pingyun001/LimeRC/STRUCTOR/RemoteController/成品零件/锂电池603450.SLDPRT

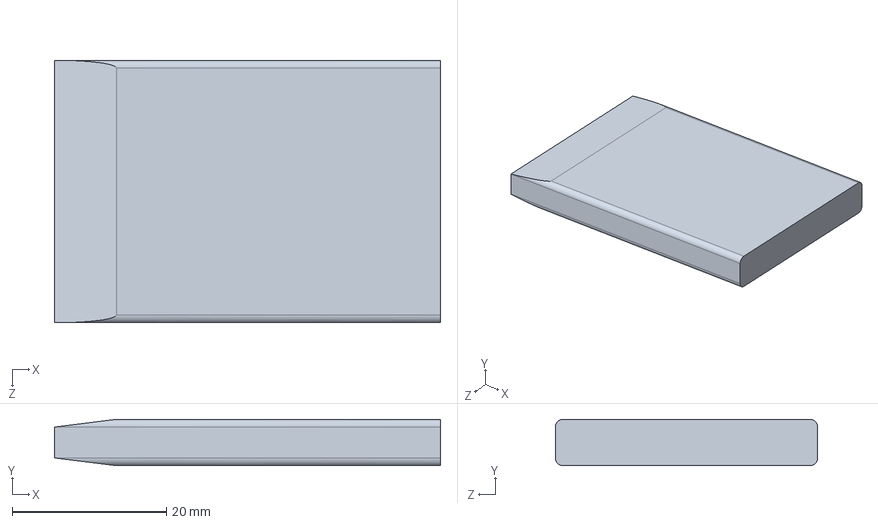
[picture p37: CAD file, 2025-12-01]
STRUCTOR/RemoteController/成品零件/锂电池603450.SLDPRT
50.0 x 6.00 x 34.0 mm
