pingyun001/LimeRC/STRUCTOR/RemoteController/打印件/摇杆帽打印.3MF

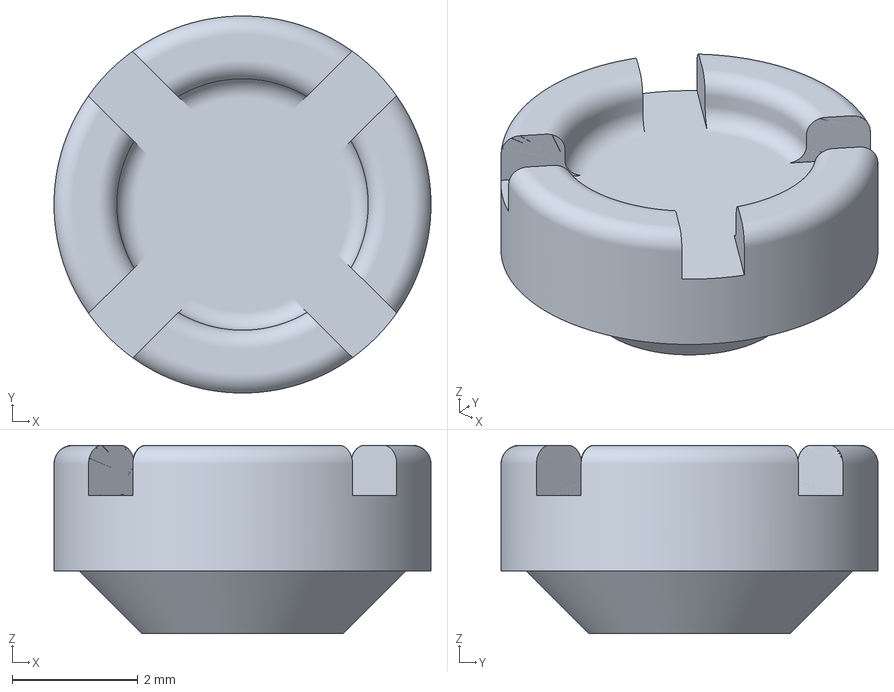
[picture p38: CAD file, 2025-12-01]
STRUCTOR/RemoteController/打印件/摇杆帽打印.3MF
6.00 x 6.00 x 3.00 mm
