pingyun001/LimeRC/STRUCTOR/ScreenSubBoard/1.3寸240屏幕焊接1.STEP

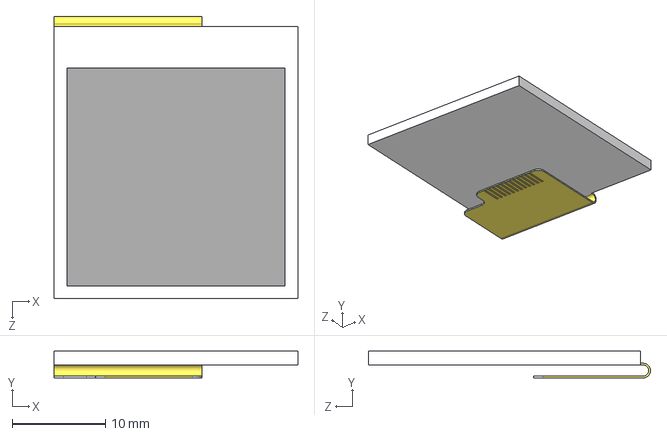
[picture p39: CAD file, 2025-12-01]
STRUCTOR/ScreenSubBoard/1.3寸240屏幕焊接1.STEP
26.2 x 2.89 x 30.3 mm
