pingyun001/LimeRC/STRUCTOR/RemoteController/侧框打印.SLDPRT

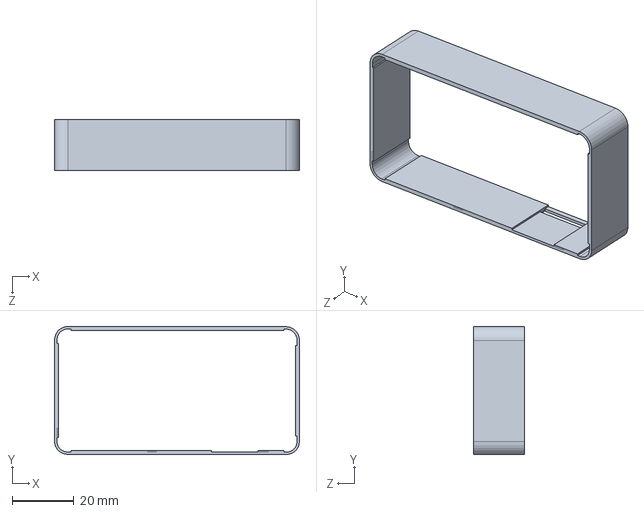
[picture p40: CAD file, 2025-12-01]
STRUCTOR/RemoteController/侧框打印.SLDPRT
79.5 x 41.5 x 16.7 mm
