pingyun001/LimeRC/STRUCTOR/RemoteController/打印件/中心打印支架上.SLDPRT

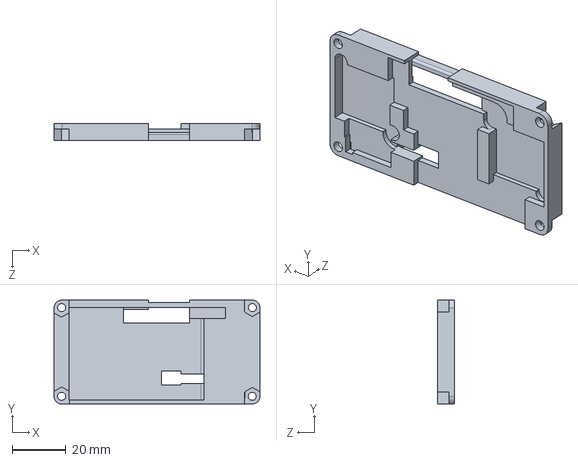
[picture p41: CAD file, 2025-12-01]
STRUCTOR/RemoteController/打印件/中心打印支架上.SLDPRT
76.7 x 38.7 x 6.40 mm
