pingyun001/LimeRC/STRUCTOR/ScreenSubBoard/3D摇杆.SLDPRT

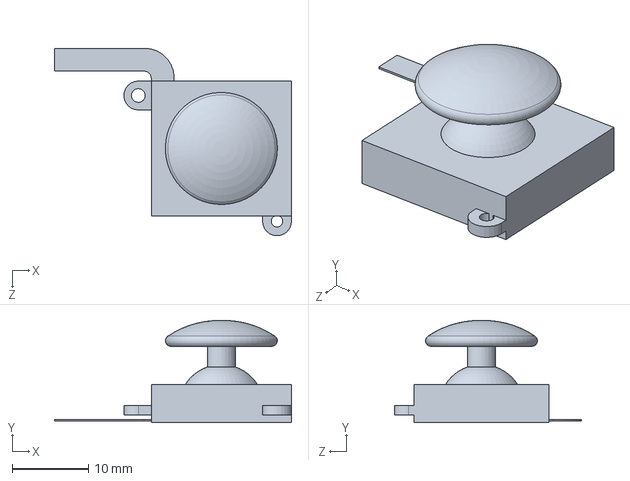
[picture p42: CAD file, 2025-12-01]
STRUCTOR/ScreenSubBoard/3D摇杆.SLDPRT
31.1 x 13.4 x 24.6 mm
