pingyun001/LimeRC/STRUCTOR/RemoteController/成品零件/锂电池102550.SLDPRT

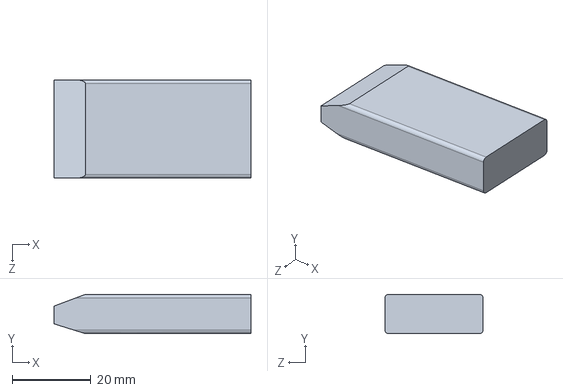
[picture p43: CAD file, 2025-12-01]
STRUCTOR/RemoteController/成品零件/锂电池102550.SLDPRT
50.0 x 10.0 x 25.0 mm
