pingyun001/LimeRC/STRUCTOR/RemoteController/打印件/底壳打印.SLDPRT

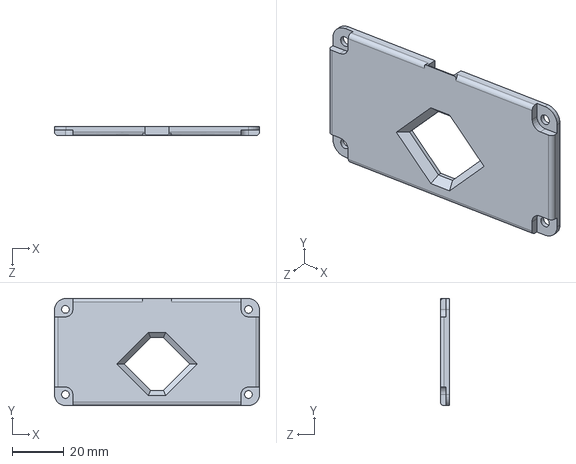
[picture p44: CAD file, 2025-12-01]
STRUCTOR/RemoteController/打印件/底壳打印.SLDPRT
79.5 x 41.5 x 3.50 mm
