pingyun001/LimeRC/STRUCTOR/ScreenSubBoard/摇杆模组PCB定位件.DXF

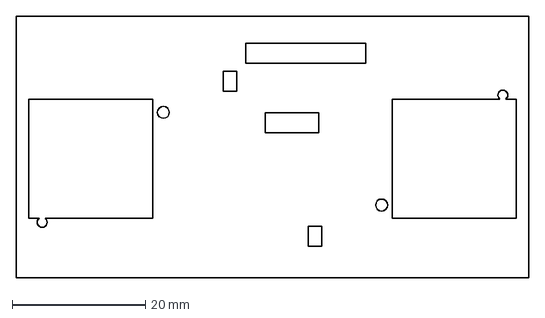
[picture p45: CAD file, 2025-12-01]
STRUCTOR/ScreenSubBoard/摇杆模组PCB定位件.DXF
77.0 x 39.2 mm
