pingyun001/LimeRC/STRUCTOR/RemoteController/打印件/中心打印支架下.SLDPRT

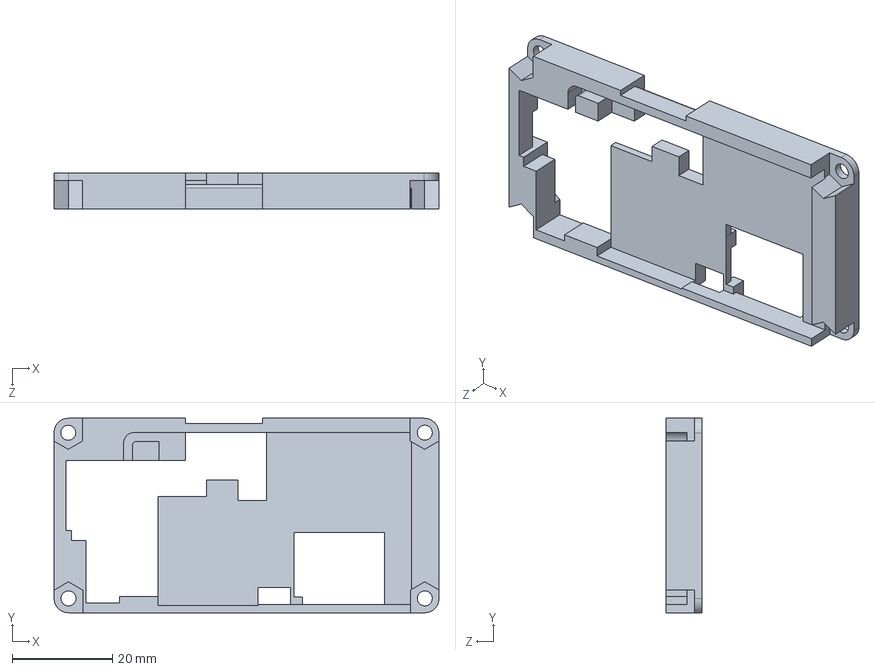
[picture p46: CAD file, 2025-12-01]
STRUCTOR/RemoteController/打印件/中心打印支架下.SLDPRT
76.7 x 38.8 x 7.10 mm
