pingyun001/LimeRC/STRUCTOR/RemoteController/打印件/顶壳打印.SLDPRT

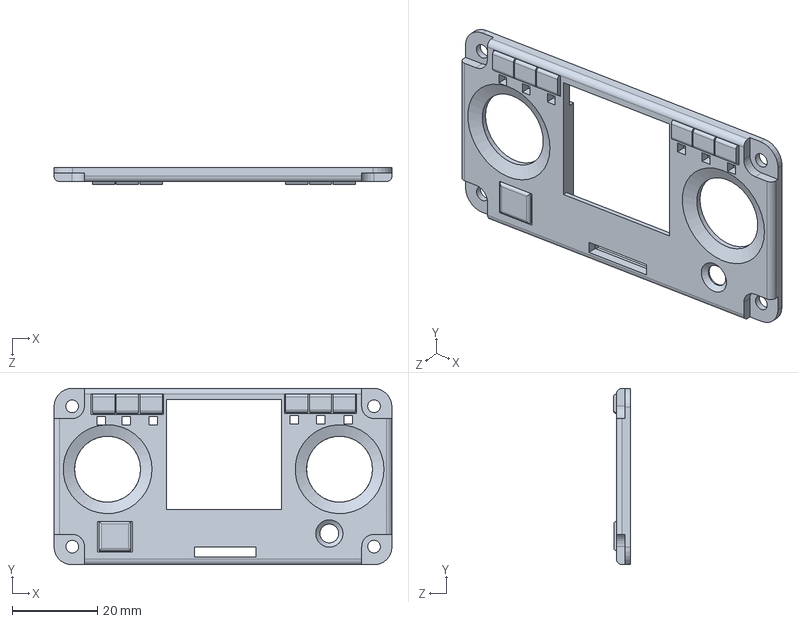
[picture p47: CAD file, 2025-12-01]
STRUCTOR/RemoteController/打印件/顶壳打印.SLDPRT
79.5 x 41.5 x 4.00 mm
