pingyun001/LimeRC/STRUCTOR/ScreenSubBoard/1.3寸240屏幕焊接.SLDPRT

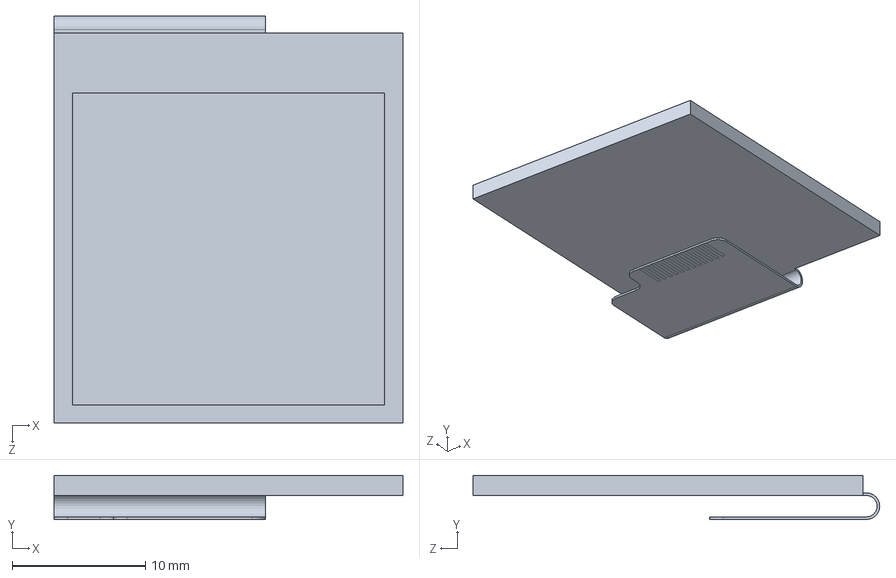
[picture p48: CAD file, 2025-12-01]
STRUCTOR/ScreenSubBoard/1.3寸240屏幕焊接.SLDPRT
26.2 x 3.30 x 30.5 mm
