pingyun001/LimeRC/SOFTWARE/LimeCam_Release/Core/Src/usart.c

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
/* Includes ------------------------------------------------------------------*/
#include "usart.h"

/* USER CODE BEGIN 0 */
#include "stdio.h"

#if defined(__ARMCC_VERSION) && (__ARMCC_VERSION > 6000000)
// V5编译器
#define COMPILER_IS_V6	1
#else
// V6编译器
#define COMPILER_IS_V5	1
#endif

#ifdef COMPILER_IS_V6
#if !defined(__MICROLIB)
__asm (".global __use_no_semihosting\n\t");
void _sys_exit(int x) //避免使用半主机模式
{
  x = x;
}
//__use_no_semihosting was requested, but _ttywrch was 
void _ttywrch(int ch)
{
    ch = ch;
}
FILE __stdout;
#endif		//!defined(__MICROLIB)

#if defined ( __GNUC__ ) && !defined (__clang__) 
#define PUTCHAR_PROTOTYPE int __io_putchar(int ch)
#else
#define PUTCHAR_PROTOTYPE int fputc(int ch, FILE *f)
#endif 
PUTCHAR_PROTOTYPE
{
  /* 实现串口发送一个字节数据的函数 */
  //serial_write(&serial1, (uint8_t)ch); //发送一个自己的数据到串口
	while((UART5 -> SR & 0X40) == 0){}
    UART5->DR = (uint8_t )ch;
  return ch;
}
#endif
#ifdef COMPILER_IS_V5
#pragma import(__use_no_semihosting)                             
struct __FILE { 
    int handle; 
}; 

FILE __stdout;          
void _sys_exit(int x) { 
    x = x; 
}
//重定向printf到串口7（A板上标注有7的位置）
int fputc(int ch, FILE *f){      
    while((UART5 -> SR & 0X40) == 0){}
    UART5->DR = (uint8_t )ch;
    return ch;
}
#endif	//(COMPILER_IS_V5)

#include <stdio.h>
#include <stdarg.h>
int LEPrintf(const char *format, ...) 
{
    char buffer[128]; // 缓冲区，用于存储格式化后的字符串
    va_list args;
    int length;

    // 初始化可变参数列表
    va_start(args, format);

    // 使用 snprintf 格式化字符串
    length = vsnprintf(buffer, sizeof(buffer), format, args);

    // 结束可变参数处理
    va_end(args);

    // 如果字符串过长，截断输出
    if (length > sizeof(buffer) - 1) {
        length = sizeof(buffer) - 1;
    }

    // 通过 UART 发送格式化后的字符串
		HAL_UART_Transmit(&huart1, (uint8_t *)"[LEP]:", 6, 500);
    HAL_UART_Transmit(&huart1, (uint8_t *)buffer, length, 500);

    return length; // 返回实际输出的字符数
}

/* USER CODE END 0 */

UART_HandleTypeDef huart5;
UART_HandleTypeDef huart1;
UART_HandleTypeDef huart2;
UART_HandleTypeDef huart3;

/* UART5 init function */
void MX_UART5_Init(void)
{

  huart5.Instance = UART5;
  huart5.Init.BaudRate = 921600;
  huart5.Init.WordLength = UART_WORDLENGTH_8B;
  huart5.Init.StopBits = UART_STOPBITS_1;
  huart5.Init.Parity = UART_PARITY_NONE;
  huart5.Init.Mode = UART_MODE_TX_RX;
  huart5.Init.HwFlowCtl = UART_HWCONTROL_NONE;
  huart5.Init.OverSampling = UART_OVERSAMPLING_16;
  if (HAL_UART_Init(&huart5) != HAL_OK)
  {
    Error_Handler();
  }
}
/* USART1 init function */

void MX_USART1_UART_Init(void)
{

  huart1.Instance = USART1;
  huart1.Init.BaudRate = 115200;
  huart1.Init.WordLength = UART_WORDLENGTH_8B;
  huart1.Init.StopBits = UART_STOPBITS_1;
  huart1.Init.Parity = UART_PARITY_NONE;
  huart1.Init.Mode = UART_MODE_TX_RX;
  huart1.Init.HwFlowCtl = UART_HWCONTROL_NONE;
  huart1.Init.OverSampling = UART_OVERSAMPLING_16;
  if (HAL_UART_Init(&huart1) != HAL_OK)
  {
    Error_Handler();
  }
}
/* USART2 init function */

void MX_USART2_UART_Init(void)
{

  huart2.Instance = USART2;
  huart2.Init.BaudRate = 115200;
  huart2.Init.WordLength = UART_WORDLENGTH_8B;
  huart2.Init.StopBits = UART_STOPBITS_1;
  huart2.Init.Parity = UART_PARITY_NONE;
  huart2.Init.Mode = UART_MODE_TX_RX;
  huart2.Init.HwFlowCtl = UART_HWCONTROL_NONE;
  huart2.Init.OverSampling = UART_OVERSAMPLING_16;
  if (HAL_UART_Init(&huart2) != HAL_OK)
  {
    Error_Handler();
  }
}
/* USART3 init function */

void MX_USART3_UART_Init(void)
{

  huart3.Instance = USART3;
  huart3.Init.BaudRate = 115200;
  huart3.Init.WordLength = UART_WORDLENGTH_8B;
  huart3.Init.StopBits = UART_STOPBITS_1;
  huart3.Init.Parity = UART_PARITY_NONE;
  huart3.Init.Mode = UART_MODE_TX_RX;
  huart3.Init.HwFlowCtl = UART_HWCONTROL_NONE;
  huart3.Init.OverSampling = UART_OVERSAMPLING_16;
  if (HAL_UART_Init(&huart3) != HAL_OK)
  {
    Error_Handler();
  }
}

void HAL_UART_MspInit(UART_HandleTypeDef* uartHandle)
{

  GPIO_InitTypeDef GPIO_InitStruct = {0};
  if(uartHandle->Instance==UART5)
  {
    /* UART5 clock enable */
    __HAL_RCC_UART5_CLK_ENABLE();

    __HAL_RCC_GPIOC_CLK_ENABLE();
    __HAL_RCC_GPIOD_CLK_ENABLE();
    /**UART5 GPIO Configuration
    PC12     ------> UART5_TX
    PD2     ------> UART5_RX
    */
    GPIO_InitStruct.Pin = GPIO_PIN_12;
    GPIO_InitStruct.Mode = GPIO_MODE_AF_PP;
    GPIO_InitStruct.Pull = GPIO_NOPULL;
    GPIO_InitStruct.Speed = GPIO_SPEED_FREQ_VERY_HIGH;
    GPIO_InitStruct.Alternate = GPIO_AF8_UART5;
    HAL_GPIO_Init(GPIOC, &GPIO_InitStruct);

    GPIO_InitStruct.Pin = GPIO_PIN_2;
    GPIO_InitStruct.Mode = GPIO_MODE_AF_PP;
    GPIO_InitStruct.Pull = GPIO_NOPULL;
    GPIO_InitStruct.Speed = GPIO_SPEED_FREQ_VERY_HIGH;
    GPIO_InitStruct.Alternate = GPIO_AF8_UART5;
    HAL_GPIO_Init(GPIOD, &GPIO_InitStruct);

  }
  else if(uartHandle->Instance==USART1)
  {
    /* USART1 clock enable */
    __HAL_RCC_USART1_CLK_ENABLE();

    __HAL_RCC_GPIOA_CLK_ENABLE();
    /**USART1 GPIO Configuration
    PA9     ------> USART1_TX
    PA10     ------> USART1_RX
    */
    GPIO_InitStruct.Pin = GPIO_PIN_9|GPIO_PIN_10;
    GPIO_InitStruct.Mode = GPIO_MODE_AF_PP;
    GPIO_InitStruct.Pull = GPIO_NOPULL;
    GPIO_InitStruct.Speed = GPIO_SPEED_FREQ_VERY_HIGH;
    GPIO_InitStruct.Alternate = GPIO_AF7_USART1;
    HAL_GPIO_Init(GPIOA, &GPIO_InitStruct);

  }
  else if(uartHandle->Instance==USART2)
  {
    /* USART2 clock enable */
    __HAL_RCC_USART2_CLK_ENABLE();

    __HAL_RCC_GPIOA_CLK_ENABLE();
    /**USART2 GPIO Configuration
    PA2     ------> USART2_TX
    PA3     ------> USART2_RX
    */
    GPIO_InitStruct.Pin = GPIO_PIN_2|GPIO_PIN_3;
    GPIO_InitStruct.Mode = GPIO_MODE_AF_PP;
    GPIO_InitStruct.Pull = GPIO_NOPULL;
    GPIO_InitStruct.Speed = GPIO_SPEED_FREQ_VERY_HIGH;
    GPIO_InitStruct.Alternate = GPIO_AF7_USART2;
    HAL_GPIO_Init(GPIOA, &GPIO_InitStruct);

  }
  else if(uartHandle->Instance==USART3)
  {
    /* USART3 clock enable */
    __HAL_RCC_USART3_CLK_ENABLE();

    __HAL_RCC_GPIOD_CLK_ENABLE();
    /**USART3 GPIO Configuration
    PD8     ------> USART3_TX
    PD9     ------> USART3_RX
    */
    GPIO_InitStruct.Pin = GPIO_PIN_8|GPIO_PIN_9;
    GPIO_InitStruct.Mode = GPIO_MODE_AF_PP;
    GPIO_InitStruct.Pull = GPIO_NOPULL;
    GPIO_InitStruct.Speed = GPIO_SPEED_FREQ_VERY_HIGH;
    GPIO_InitStruct.Alternate = GPIO_AF7_USART3;
    HAL_GPIO_Init(GPIOD, &GPIO_InitStruct);

    /* USART3 interrupt Init */
    HAL_NVIC_SetPriority(USART3_IRQn, 10, 0);
    HAL_NVIC_EnableIRQ(USART3_IRQn);
  }
}

void HAL_UART_MspDeInit(UART_HandleTypeDef* uartHandle)
{

  if(uartHandle->Instance==UART5)
  {
    /* Peripheral clock disable */
    __HAL_RCC_UART5_CLK_DISABLE();

    /**UART5 GPIO Configuration
    PC12     ------> UART5_TX
    PD2     ------> UART5_RX
    */
    HAL_GPIO_DeInit(GPIOC, GPIO_PIN_12);

    HAL_GPIO_DeInit(GPIOD, GPIO_PIN_2);

  }
  else if(uartHandle->Instance==USART1)
  {
    /* Peripheral clock disable */
    __HAL_RCC_USART1_CLK_DISABLE();

    /**USART1 GPIO Configuration
    PA9     ------> USART1_TX
    PA10     ------> USART1_RX
    */
    HAL_GPIO_DeInit(GPIOA, GPIO_PIN_9|GPIO_PIN_10);

  }
  else if(uartHandle->Instance==USART2)
  {
    /* Peripheral clock disable */
    __HAL_RCC_USART2_CLK_DISABLE();

    /**USART2 GPIO Configuration
    PA2     ------> USART2_TX
    PA3     ------> USART2_RX
    */
    HAL_GPIO_DeInit(GPIOA, GPIO_PIN_2|GPIO_PIN_3);

  }
  else if(uartHandle->Instance==USART3)
  {
    /* Peripheral clock disable */
    __HAL_RCC_USART3_CLK_DISABLE();

    /**USART3 GPIO Configuration
    PD8     ------> USART3_TX
    PD9     ------> USART3_RX
    */
    HAL_GPIO_DeInit(GPIOD, GPIO_PIN_8|GPIO_PIN_9);

    /* USART3 interrupt Deinit */
    HAL_NVIC_DisableIRQ(USART3_IRQn);
  }
}
