pingyun001/LimeRC/SOFTWARE/LimeMainBoard_Release/Core/Src/usart.c

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
/* Includes ------------------------------------------------------------------*/
#include "usart.h"

/* USER CODE BEGIN 0 */
#include <stdio.h>
#include <stdarg.h>
int LEprintf(const char *format, ...)
{
    char buffer[128];
    va_list args;
    int length;

    va_start(args, format);

    length = vsnprintf(buffer, sizeof(buffer), format, args);

    va_end(args);

    if (length > sizeof(buffer) - 1) {
        length = sizeof(buffer) - 1;
    }

    HAL_UART_Transmit(&huart1, (uint8_t *)buffer, length, HAL_MAX_DELAY);

    return length;
}

#include "lvgl.h"
#include <string.h>
void lime_lvgl_print(lv_log_level_t level, const char * buf)
{
	LEprintf("%d,%s", level, buf);
}

/* USER CODE END 0 */

UART_HandleTypeDef huart4;
UART_HandleTypeDef huart1;
DMA_HandleTypeDef hdma_uart4_rx;

/* UART4 init function */
void MX_UART4_Init(void)
{

  huart4.Instance = UART4;
  huart4.Init.BaudRate = 115200;
  huart4.Init.WordLength = UART_WORDLENGTH_8B;
  huart4.Init.StopBits = UART_STOPBITS_1;
  huart4.Init.Parity = UART_PARITY_NONE;
  huart4.Init.Mode = UART_MODE_TX_RX;
  huart4.Init.HwFlowCtl = UART_HWCONTROL_NONE;
  huart4.Init.OverSampling = UART_OVERSAMPLING_16;
  huart4.Init.OneBitSampling = UART_ONE_BIT_SAMPLE_DISABLE;
  huart4.Init.ClockPrescaler = UART_PRESCALER_DIV1;
  huart4.AdvancedInit.AdvFeatureInit = UART_ADVFEATURE_NO_INIT;
  if (HAL_UART_Init(&huart4) != HAL_OK)
  {
    Error_Handler();
  }
  if (HAL_UARTEx_SetTxFifoThreshold(&huart4, UART_TXFIFO_THRESHOLD_1_8) != HAL_OK)
  {
    Error_Handler();
  }
  if (HAL_UARTEx_SetRxFifoThreshold(&huart4, UART_RXFIFO_THRESHOLD_1_8) != HAL_OK)
  {
    Error_Handler();
  }
  if (HAL_UARTEx_DisableFifoMode(&huart4) != HAL_OK)
  {
    Error_Handler();
  }
}
/* USART1 init function */

void MX_USART1_UART_Init(void)
{

  huart1.Instance = USART1;
  huart1.Init.BaudRate = 921600;
  huart1.Init.WordLength = UART_WORDLENGTH_8B;
  huart1.Init.StopBits = UART_STOPBITS_1;
  huart1.Init.Parity = UART_PARITY_NONE;
  huart1.Init.Mode = UART_MODE_TX_RX;
  huart1.Init.HwFlowCtl = UART_HWCONTROL_NONE;
  huart1.Init.OverSampling = UART_OVERSAMPLING_16;
  huart1.Init.OneBitSampling = UART_ONE_BIT_SAMPLE_DISABLE;
  huart1.Init.ClockPrescaler = UART_PRESCALER_DIV1;
  huart1.AdvancedInit.AdvFeatureInit = UART_ADVFEATURE_NO_INIT;
  if (HAL_UART_Init(&huart1) != HAL_OK)
  {
    Error_Handler();
  }
  if (HAL_UARTEx_SetTxFifoThreshold(&huart1, UART_TXFIFO_THRESHOLD_1_8) != HAL_OK)
  {
    Error_Handler();
  }
  if (HAL_UARTEx_SetRxFifoThreshold(&huart1, UART_RXFIFO_THRESHOLD_1_8) != HAL_OK)
  {
    Error_Handler();
  }
  if (HAL_UARTEx_DisableFifoMode(&huart1) != HAL_OK)
  {
    Error_Handler();
  }
}

void HAL_UART_MspInit(UART_HandleTypeDef* uartHandle)
{

  GPIO_InitTypeDef GPIO_InitStruct = {0};
  RCC_PeriphCLKInitTypeDef PeriphClkInitStruct = {0};
  if(uartHandle->Instance==UART4)
  {
  /** Initializes the peripherals clock
  */
    PeriphClkInitStruct.PeriphClockSelection = RCC_PERIPHCLK_UART4;
    PeriphClkInitStruct.Usart234578ClockSelection = RCC_USART234578CLKSOURCE_D2PCLK1;
    if (HAL_RCCEx_PeriphCLKConfig(&PeriphClkInitStruct) != HAL_OK)
    {
      Error_Handler();
    }

    /* UART4 clock enable */
    __HAL_RCC_UART4_CLK_ENABLE();

    __HAL_RCC_GPIOD_CLK_ENABLE();
    /**UART4 GPIO Configuration
    PD0     ------> UART4_RX
    PD1     ------> UART4_TX
    */
    GPIO_InitStruct.Pin = GPIO_PIN_0|GPIO_PIN_1;
    GPIO_InitStruct.Mode = GPIO_MODE_AF_PP;
    GPIO_InitStruct.Pull = GPIO_NOPULL;
    GPIO_InitStruct.Speed = GPIO_SPEED_FREQ_LOW;
    GPIO_InitStruct.Alternate = GPIO_AF8_UART4;
    HAL_GPIO_Init(GPIOD, &GPIO_InitStruct);

    /* UART4 DMA Init */
    /* UART4_RX Init */
    hdma_uart4_rx.Instance = DMA1_Stream1;
    hdma_uart4_rx.Init.Request = DMA_REQUEST_UART4_RX;
    hdma_uart4_rx.Init.Direction = DMA_PERIPH_TO_MEMORY;
    hdma_uart4_rx.Init.PeriphInc = DMA_PINC_DISABLE;
    hdma_uart4_rx.Init.MemInc = DMA_MINC_ENABLE;
    hdma_uart4_rx.Init.PeriphDataAlignment = DMA_PDATAALIGN_BYTE;
    hdma_uart4_rx.Init.MemDataAlignment = DMA_MDATAALIGN_BYTE;
    hdma_uart4_rx.Init.Mode = DMA_NORMAL;
    hdma_uart4_rx.Init.Priority = DMA_PRIORITY_LOW;
    hdma_uart4_rx.Init.FIFOMode = DMA_FIFOMODE_DISABLE;
    if (HAL_DMA_Init(&hdma_uart4_rx) != HAL_OK)
    {
      Error_Handler();
    }

    __HAL_LINKDMA(uartHandle,hdmarx,hdma_uart4_rx);

    /* UART4 interrupt Init */
    HAL_NVIC_SetPriority(UART4_IRQn, 8, 0);
    HAL_NVIC_EnableIRQ(UART4_IRQn);
  }
  else if(uartHandle->Instance==USART1)
  {
  /** Initializes the peripherals clock
  */
    PeriphClkInitStruct.PeriphClockSelection = RCC_PERIPHCLK_USART1;
    PeriphClkInitStruct.Usart16ClockSelection = RCC_USART16CLKSOURCE_D2PCLK2;
    if (HAL_RCCEx_PeriphCLKConfig(&PeriphClkInitStruct) != HAL_OK)
    {
      Error_Handler();
    }

    /* USART1 clock enable */
    __HAL_RCC_USART1_CLK_ENABLE();

    __HAL_RCC_GPIOA_CLK_ENABLE();
    /**USART1 GPIO Configuration
    PA9     ------> USART1_TX
    PA10     ------> USART1_RX
    */
    GPIO_InitStruct.Pin = GPIO_PIN_9|GPIO_PIN_10;
    GPIO_InitStruct.Mode = GPIO_MODE_AF_PP;
    GPIO_InitStruct.Pull = GPIO_NOPULL;
    GPIO_InitStruct.Speed = GPIO_SPEED_FREQ_LOW;
    GPIO_InitStruct.Alternate = GPIO_AF7_USART1;
    HAL_GPIO_Init(GPIOA, &GPIO_InitStruct);

  }
}

void HAL_UART_MspDeInit(UART_HandleTypeDef* uartHandle)
{

  if(uartHandle->Instance==UART4)
  {
    /* Peripheral clock disable */
    __HAL_RCC_UART4_CLK_DISABLE();

    /**UART4 GPIO Configuration
    PD0     ------> UART4_RX
    PD1     ------> UART4_TX
    */
    HAL_GPIO_DeInit(GPIOD, GPIO_PIN_0|GPIO_PIN_1);

    /* UART4 DMA DeInit */
    HAL_DMA_DeInit(uartHandle->hdmarx);

    /* UART4 interrupt Deinit */
    HAL_NVIC_DisableIRQ(UART4_IRQn);
  }
  else if(uartHandle->Instance==USART1)
  {
    /* Peripheral clock disable */
    __HAL_RCC_USART1_CLK_DISABLE();

    /**USART1 GPIO Configuration
    PA9     ------> USART1_TX
    PA10     ------> USART1_RX
    */
    HAL_GPIO_DeInit(GPIOA, GPIO_PIN_9|GPIO_PIN_10);

  }
}
