pingyun001/LimeRC/SOFTWARE/LimeCam_Release/Bsp/Lime_ov2640map.h

/**
 ****************************************************************************************************
 * @file        atk_mc2640_cfg.h
 * @author      正点原子团队(ALIENTEK)
 * @version     V1.0
 * @date        2022-06-21
 * @brief       ATK-MC2640模块寄存器配置
 * @license     Copyright (c) 2020-2032, 广州市星翼电子科技有限公司
 ****************************************************************************************************
 * @attention
 *
 * 实验平台:正点原子 Mini Pro H750开发板
 * 在线视频:www.yuanzige.com
 * 技术论坛:www.openedv.com
 * 公司网址:www.alientek.com
 * 购买地址:openedv.taobao.com
 *
 ****************************************************************************************************
 */

#ifndef __ATK_MC2640_CFG_H
#define __ATK_MC2640_CFG_H

#include "main.h"

/* 选择ATK-MC2640模块启用的寄存器块
 * 当寄存器0xFF=00时，启用DSP寄存器块
 * 当寄存器0xFF=01时，启用Sensor寄存器块
 */
#define LIME_OV2640_REG_BANK_SEL  LIME_OV2640_REG_DSP_RA_DLMT

/* ATK-MC2640模块DSP寄存器块 */
#define LIME_OV2640_REG_DSP_R_BYPASS         0x05
#define LIME_OV2640_REG_DSP_Qs               0x44
#define LIME_OV2640_REG_DSP_CTRLI            0x50
#define LIME_OV2640_REG_DSP_HSIZE            0x51
#define LIME_OV2640_REG_DSP_VSIZE            0x52
#define LIME_OV2640_REG_DSP_XOFFL            0x53
#define LIME_OV2640_REG_DSP_YOFFL            0x54
#define LIME_OV2640_REG_DSP_VHYX             0x55
#define LIME_OV2640_REG_DSP_DPRP             0x56
#define LIME_OV2640_REG_DSP_TEST             0x57
#define LIME_OV2640_REG_DSP_ZMOW             0x5A
#define LIME_OV2640_REG_DSP_ZMOH             0x5B
#define LIME_OV2640_REG_DSP_ZMHH             0x5C
#define LIME_OV2640_REG_DSP_BPADDR           0x7C
#define LIME_OV2640_REG_DSP_BPDATA           0x7D
#define LIME_OV2640_REG_DSP_CTRL2            0x86
#define LIME_OV2640_REG_DSP_CTRL3            0x87
#define LIME_OV2640_REG_DSP_SIZEL            0x8C
#define LIME_OV2640_REG_DSP_HSIZE8           0xC0
#define LIME_OV2640_REG_DSP_VSIZE8           0xC1
#define LIME_OV2640_REG_DSP_CTRL0            0xC2
#define LIME_OV2640_REG_DSP_CTRL1            0xC3
#define LIME_OV2640_REG_DSP_R_DVP_SP         0xD3
#define LIME_OV2640_REG_DSP_IMAGE_MODE       0xDA
#define LIME_OV2640_REG_DSP_RESET            0xE0
#define LIME_OV2640_REG_DSP_MS_SP            0xF0
#define LIME_OV2640_REG_DSP_SS_ID            0xF7
#define LIME_OV2640_REG_DSP_SS_CTRL          0xF8
#define LIME_OV2640_REG_DSP_MC_BIST          0xF9
#define LIME_OV2640_REG_DSP_MC_AL            0xFA
#define LIME_OV2640_REG_DSP_MC_AH            0xFB
#define LIME_OV2640_REG_DSP_MC_D             0xFC
#define LIME_OV2640_REG_DSP_P_CMD            0xFD
#define LIME_OV2640_REG_DSP_P_STATUS         0xFE
#define LIME_OV2640_REG_DSP_RA_DLMT          0xFF

/* ATK-MC2640模块Sensor寄存器块 */
#define LIME_OV2640_REG_SENSOR_GAIN          0x00
#define LIME_OV2640_REG_SENSOR_COM1          0x03
#define LIME_OV2640_REG_SENSOR_REG04         0x04
#define LIME_OV2640_REG_SENSOR_REG08         0x08
#define LIME_OV2640_REG_SENSOR_COM2          0x09
#define LIME_OV2640_REG_SENSOR_PIDH          0x0A
#define LIME_OV2640_REG_SENSOR_PIDL          0x0B
#define LIME_OV2640_REG_SENSOR_COM3          0x0C
#define LIME_OV2640_REG_SENSOR_COM4          0x0D
#define LIME_OV2640_REG_SENSOR_AEC           0x10
#define LIME_OV2640_REG_SENSOR_CLKRC         0x11
#define LIME_OV2640_REG_SENSOR_COM7          0x12
#define LIME_OV2640_REG_SENSOR_COM8          0x13
#define LIME_OV2640_REG_SENSOR_COM9          0x14
#define LIME_OV2640_REG_SENSOR_COM10         0x15
#define LIME_OV2640_REG_SENSOR_HREFST        0x17
#define LIME_OV2640_REG_SENSOR_HREFEND       0x18
#define LIME_OV2640_REG_SENSOR_VSTRT         0x19
#define LIME_OV2640_REG_SENSOR_VEND          0x1A
#define LIME_OV2640_REG_SENSOR_MIDH          0x1C
#define LIME_OV2640_REG_SENSOR_MIDL          0x1D
#define LIME_OV2640_REG_SENSOR_AEW           0x24
#define LIME_OV2640_REG_SENSOR_AEB           0x25
#define LIME_OV2640_REG_SENSOR_VV            0x26
#define LIME_OV2640_REG_SENSOR_REG2A         0x2A
#define LIME_OV2640_REG_SENSOR_FRARL         0x2B
#define LIME_OV2640_REG_SENSOR_ADDVSL        0x2D
#define LIME_OV2640_REG_SENSOR_ADDVSH        0x2E
#define LIME_OV2640_REG_SENSOR_YAVG          0x2F
#define LIME_OV2640_REG_SENSOR_HSDY          0x30
#define LIME_OV2640_REG_SENSOR_HEDY          0x31
#define LIME_OV2640_REG_SENSOR_REG32         0x32
#define LIME_OV2640_REG_SENSOR_ARCOM2        0x34
#define LIME_OV2640_REG_SENSOR_REG45         0x45
#define LIME_OV2640_REG_SENSOR_FLL           0x46
#define LIME_OV2640_REG_SENSOR_FLH           0x47
#define LIME_OV2640_REG_SENSOR_COM19         0x48
#define LIME_OV2640_REG_SENSOR_ZOOMS         0x49
#define LIME_OV2640_REG_SENSOR_COM22         0x4B
#define LIME_OV2640_REG_SENSOR_COM25         0x4E
#define LIME_OV2640_REG_SENSOR_BD50          0x4F
#define LIME_OV2640_REG_SENSOR_BD60          0x50
#define LIME_OV2640_REG_SENSOR_REG5D         0x5D
#define LIME_OV2640_REG_SENSOR_REG5E         0x5E
#define LIME_OV2640_REG_SENSOR_REG5F         0x5F
#define LIME_OV2640_REG_SENSOR_REG60         0x60
#define LIME_OV2640_REG_SENSOR_HISTO_LOW     0x61
#define LIME_OV2640_REG_SENSOR_HISTO_HIGH    0x62


const uint8_t atk_mc2640_set_yuv422_cfg[][2] = {
    {0xFF, 0x00},
    {0xDA, 0x10},
    {0xD7, 0x03},
    {0xDF, 0x00},
    {0x33, 0x80},
    {0x3C, 0x40},
    {0xE1, 0x77},
    {0x00, 0x00},
};

const uint8_t atk_mc2640_set_jpeg_cfg[][2] = {
    {0xFF, 0x01},
    {0xE0, 0x14},
    {0xE1, 0x77},
    {0xE5, 0x1F},
    {0xD7, 0x03},
    {0xDA, 0x10},
    {0xE0, 0x00},
};

const uint8_t atk_mc2640_set_rgb565_cfg[][2] = {
    {0xFF, 0x00},
    {0xDA, 0x09},
    {0xD7, 0x03},
    {0xDF, 0x02},
    {0x33, 0xA0},
    {0x3C, 0x00},
    {0xE1, 0x67},
    {0xFF, 0x01},
    {0xE0, 0x00},
    {0xE1, 0x00},
    {0xE5, 0x00},
    {0xD7, 0x00},
    {0xDA, 0x00},
    {0xE0, 0x00},
};

const uint8_t Lime_ov2640_SVGA_Config[][2]=
{

	{0xff, 0x01},  // 设置 sensor 寄存器组
	{0x12, 0x80},  // 复位全部寄存
	 
	{0xFF, 0x00},
	{0x2C, 0xFF},
	{0x2E, 0xDF},
	{0xFF, 0x01},
	{0x3C, 0x32},
	{0x11, 0x00},
	{0x09, 0x02},
	{0x04, 0x28},	//翻转0xF8
	{0x13, 0xE5},
	{0x14, 0x48},
	{0x2C, 0x0C},
	{0x33, 0x78},
	{0x3A, 0x33},
	{0x3B, 0xFB},
	{0x3E, 0x00},
	{0x43, 0x11},
	{0x16, 0x10},
	{0x39, 0x92},
	{0x35, 0xDA},
	{0x22, 0x1A},
	{0x37, 0xC3},
	{0x23, 0x00},
	{0x34, 0xC0},
	{0x36, 0x1A},
	{0x06, 0x88},
	{0x07, 0xC0},
	{0x0D, 0x87},
	{0x0E, 0x41},
	{0x4C, 0x00},
	{0x48, 0x00},
	{0x5B, 0x00},
	{0x42, 0x03},
	{0x4A, 0x81},
	{0x21, 0x99},
	{0x24, 0x40},
	{0x25, 0x38},
	{0x26, 0x82},
	{0x5C, 0x00},
	{0x63, 0x00},
	{0x46, 0x22},
	{0x0C, 0x3C},
	{0x61, 0x70},
	{0x62, 0x80},
	{0x7C, 0x05},
	{0x20, 0x80},
	{0x28, 0x30},
	{0x6C, 0x00},
	{0x6D, 0x80},
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
	
	{0,    0},	// 结束	
};

#endif
